Mizuseki-Lab/microdrive/variations/wide_arms/wideArm-far.stl

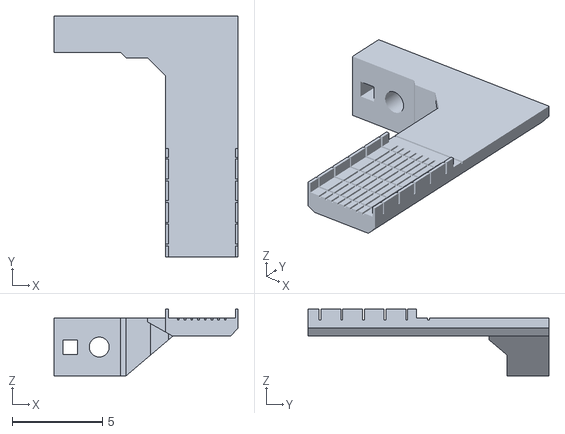
[picture p15: CAD file, 2018-05-21]
variations/wide_arms/wideArm-far.stl
10.2 x 13.3 x 3.70
