Mizuseki-Lab/microdrive/ver181005/arm-side-flip-thick.stl

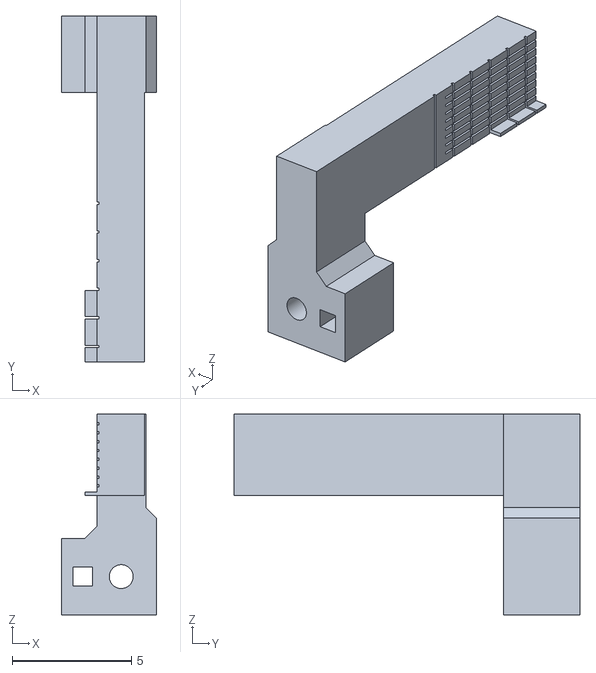
[picture p16: CAD file, 2021-01-04]
ver181005/arm-side-flip-thick.stl
3.98 x 14.5 x 8.40
