Mizuseki-Lab/microdrive/basic/attachment.stl

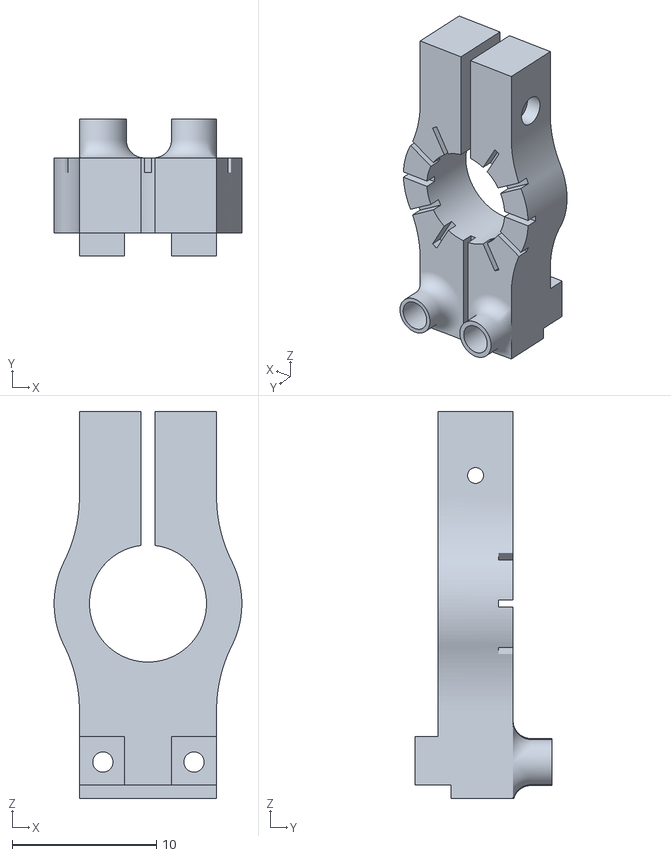
[picture p17: CAD file, 2018-05-21]
basic/attachment.stl
13.0 x 9.50 x 26.8
