Mizuseki-Lab/microdrive/variations/arm-thinTip.stl

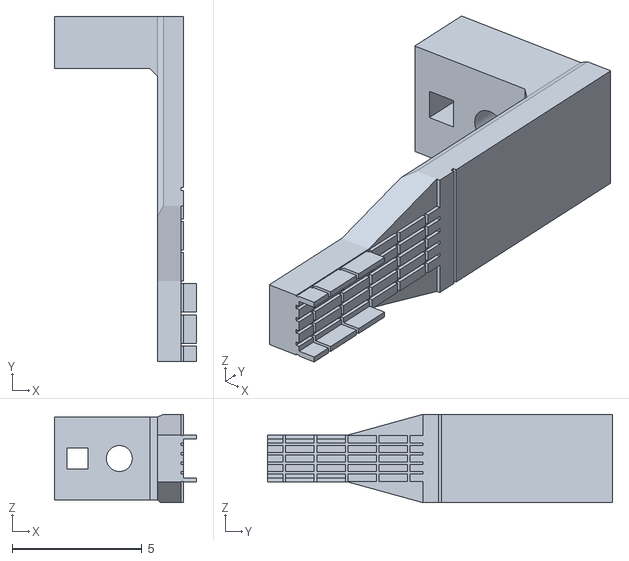
[picture p18: CAD file, 2018-05-21]
variations/arm-thinTip.stl
5.47 x 13.3 x 3.41
