Mizuseki-Lab/microdrive/variations/w_nut/arm.stl

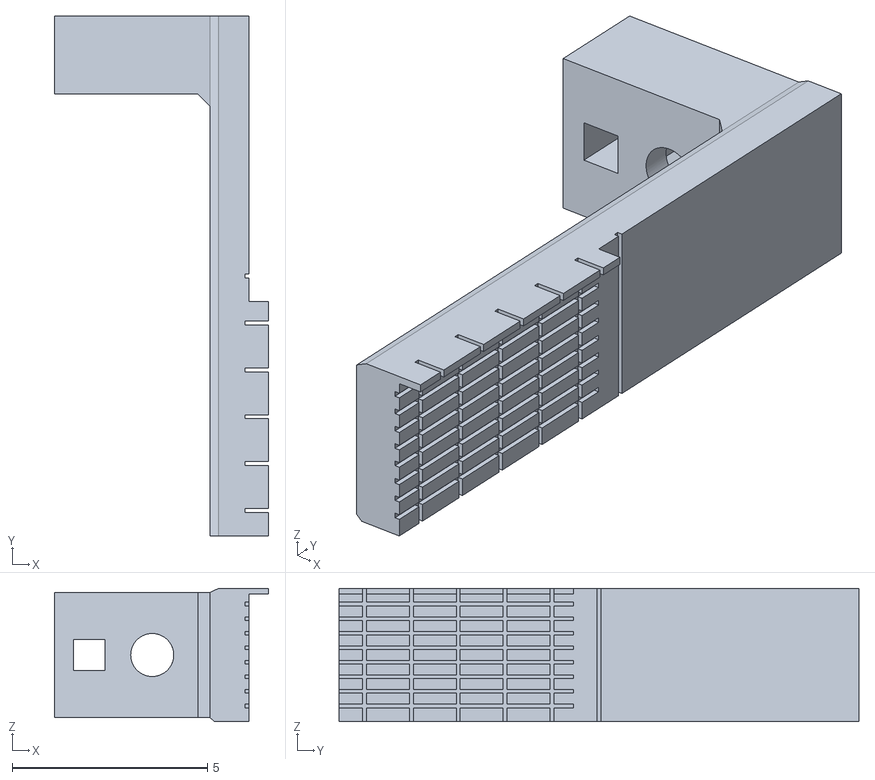
[picture p19: CAD file, 2018-05-21]
variations/w_nut/arm.stl
5.47 x 13.3 x 3.41
