Mizuseki-Lab/microdrive/variations/wide_arms/wideArm.stl

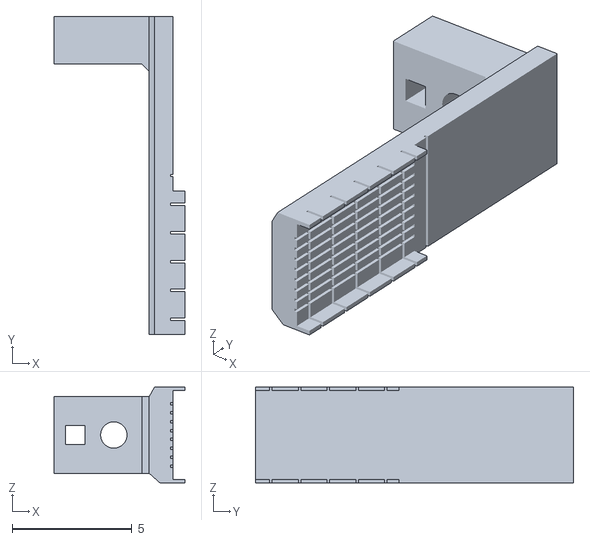
[picture p20: CAD file, 2018-05-21]
variations/wide_arms/wideArm.stl
5.47 x 13.3 x 4.00
