Mizuseki-Lab/microdrive/ver181005/base.stl

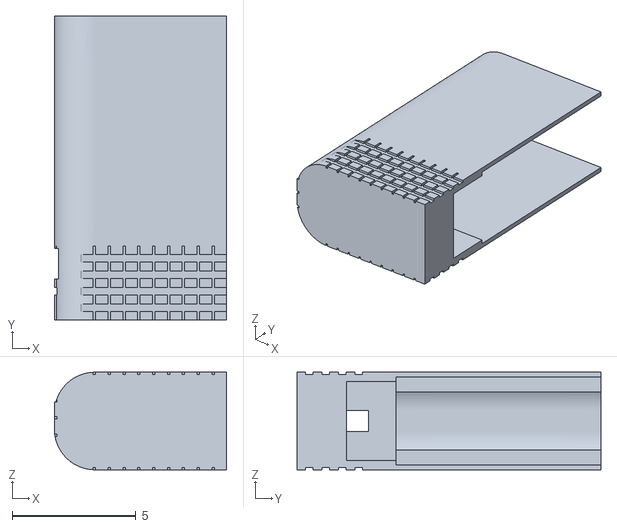
[picture p21: CAD file, 2021-01-04]
ver181005/base.stl
6.97 x 12.3 x 3.95
