Mizuseki-Lab/microdrive/basic/drive.stl

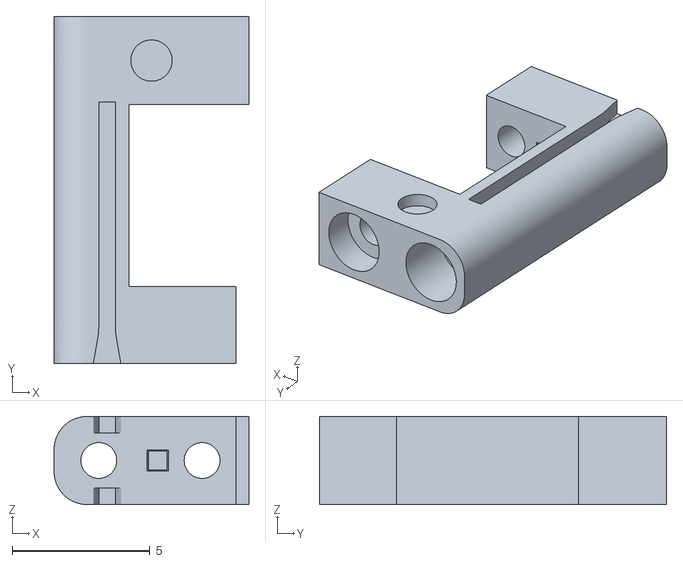
[picture p22: CAD file, 2018-05-21]
basic/drive.stl
7.07 x 12.6 x 3.20
