Mizuseki-Lab/microdrive/variations/temporal-support.stl

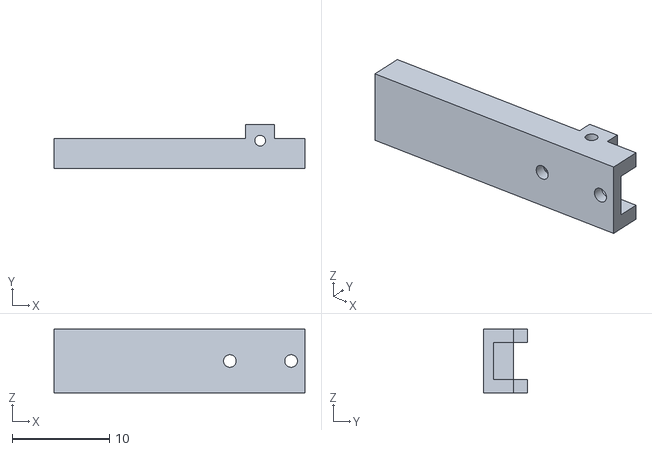
[picture p23: CAD file, 2018-05-21]
variations/temporal-support.stl
25.9 x 4.50 x 6.55
