Mizuseki-Lab/microdrive/ver181005/holder-mirror.stl

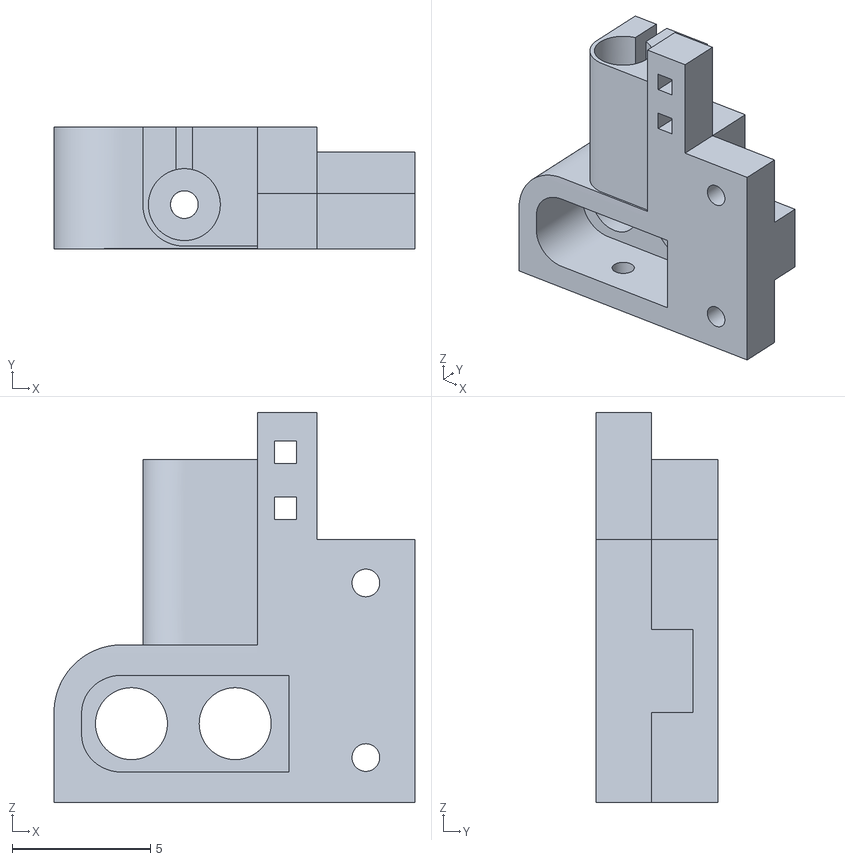
[picture p24: CAD file, 2021-01-04]
ver181005/holder-mirror.stl
13.0 x 4.40 x 14.1
