Mizuseki-Lab/microdrive/variations/base-side.stl

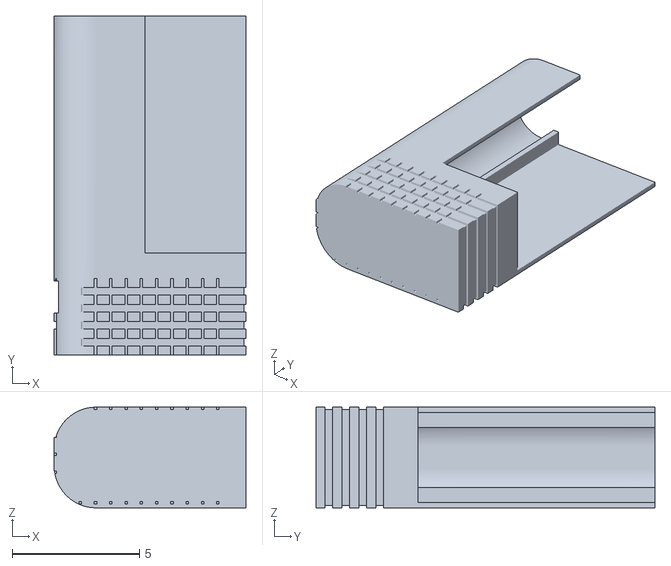
[picture p25: CAD file, 2018-05-21]
variations/base-side.stl
7.52 x 13.3 x 3.95
