Mizuseki-Lab/microdrive/ver181005/holder-far.stl

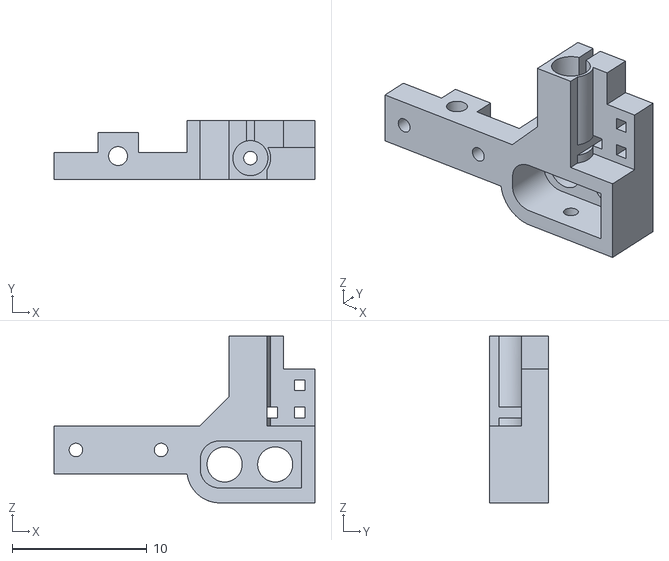
[picture p26: CAD file, 2021-01-04]
ver181005/holder-far.stl
19.4 x 4.40 x 12.4
