Mizuseki-Lab/microdrive/ver181005/arm-perpendicular-thick.stl

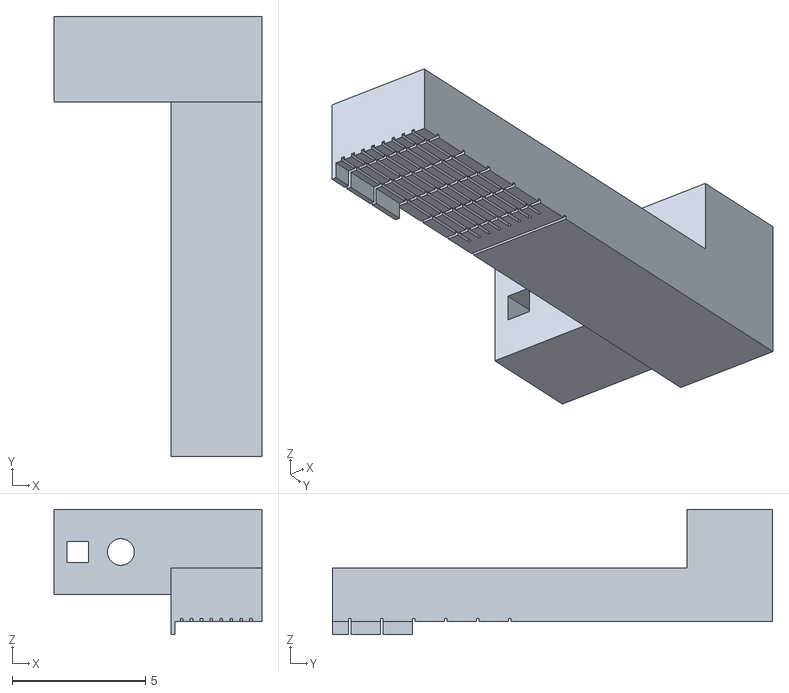
[picture p27: CAD file, 2021-01-04]
ver181005/arm-perpendicular-thick.stl
7.78 x 16.5 x 4.70
