Mizuseki-Lab/microdrive/ver181005/drive-rev2.stl

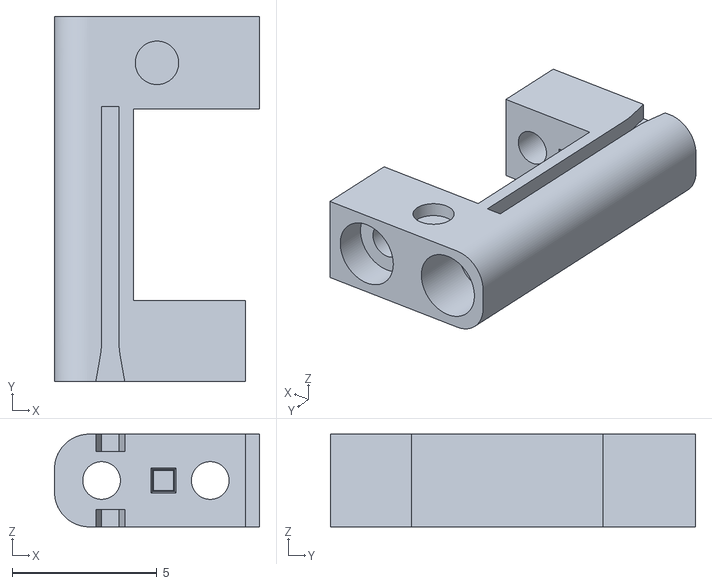
[picture p28: CAD file, 2021-01-04]
ver181005/drive-rev2.stl
7.07 x 12.6 x 3.20
