Mizuseki-Lab/microdrive/ver181005/variangle-attachment_linker.stl

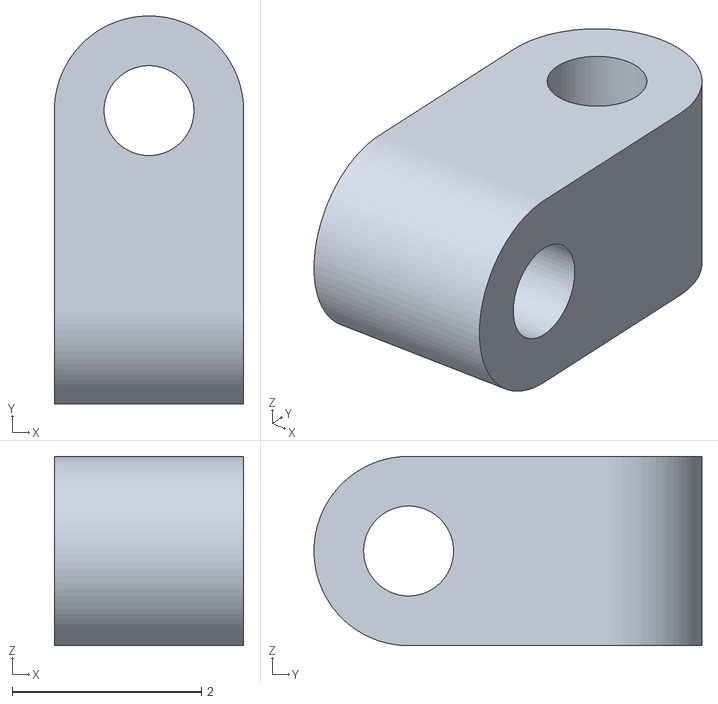
[picture p29: CAD file, 2021-01-04]
ver181005/variangle-attachment_linker.stl
2.00 x 4.10 x 2.00
